AcidSepp/ArpEverywhere/pcb/arpEverywhere/arpEverywhere.kicad_sch

## KiCad design pcb/arpEverywhere/arpEverywhere.kicad_sch (2026-10-02)

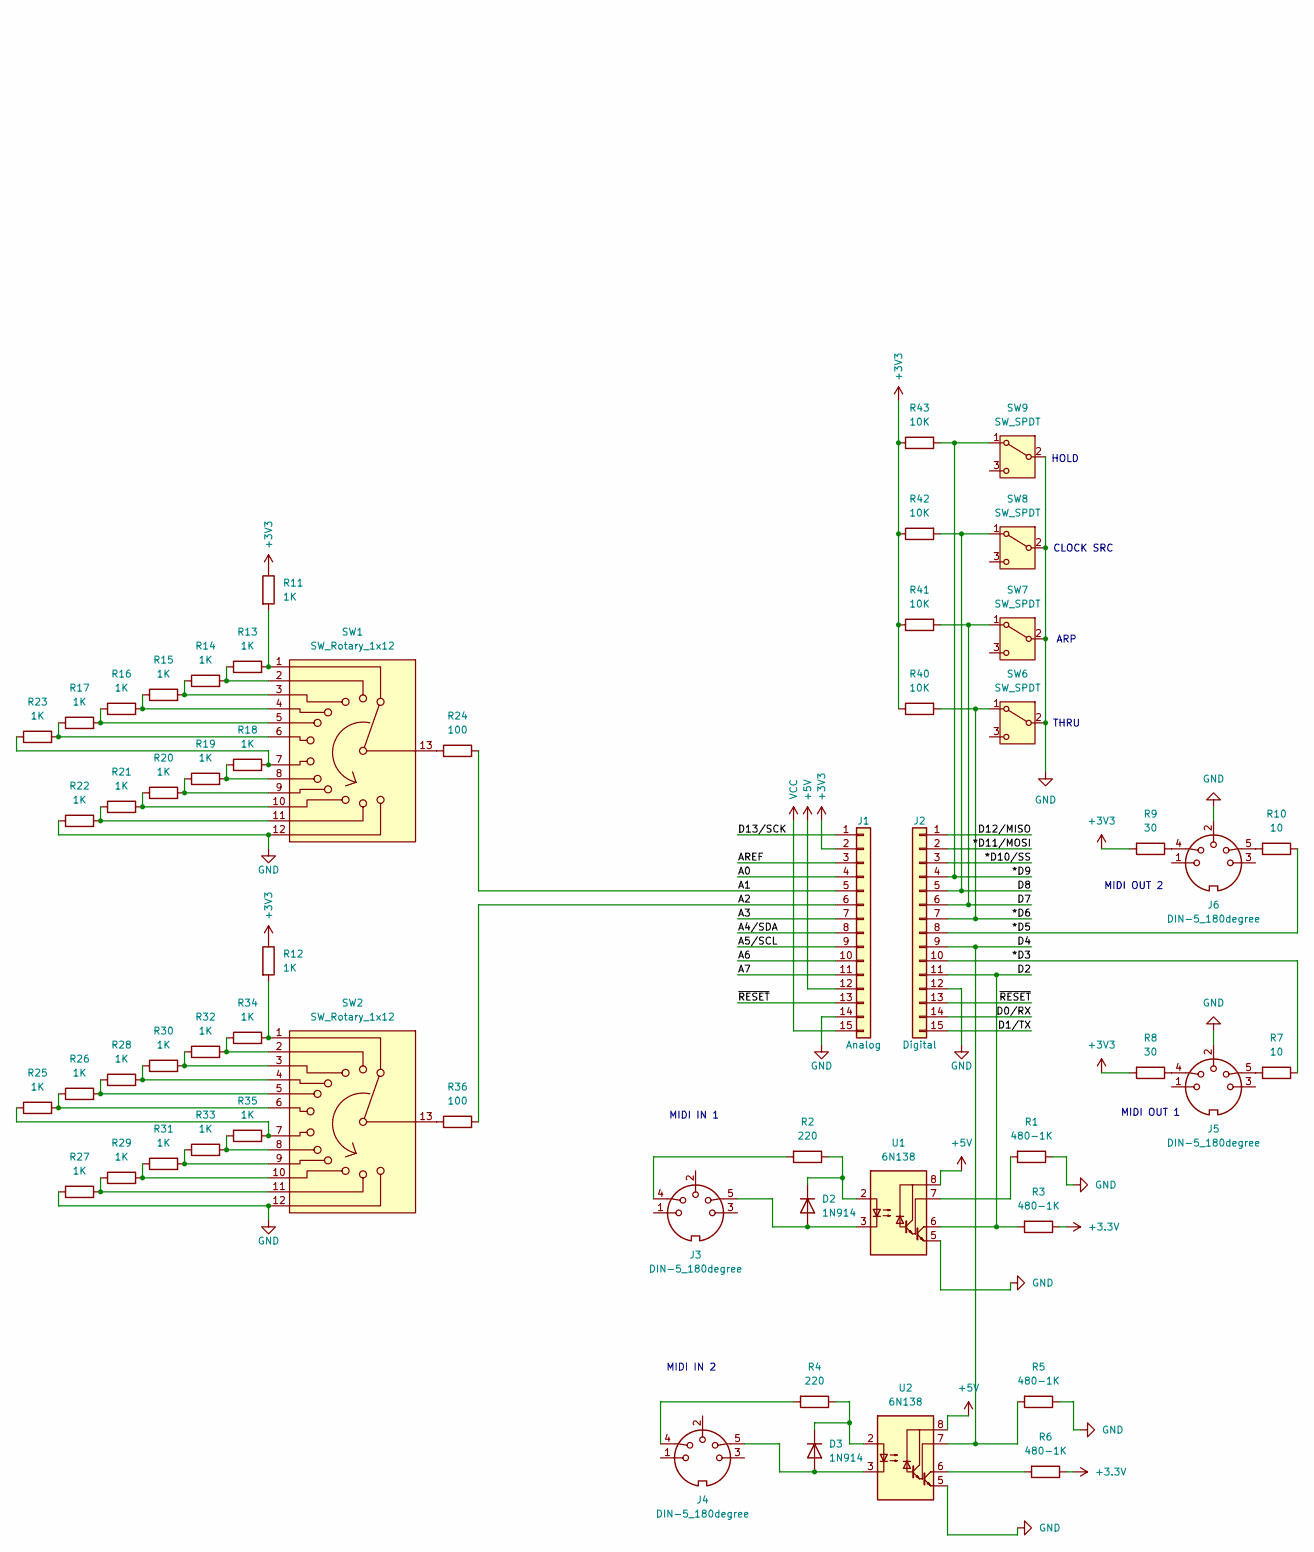
[picture p4: schematic arpEverywhere.kicad_sch, part in row 2, column 1]

Parts:
D2, D3: 1N914; D_DO-35_SOD27_P7.62mm_Horizontal
J1: Analog; PinHeader_1x15_P2.54mm_Vertical
J2: Digital; PinHeader_1x15_P2.54mm_Vertical
J3, J4, J5, J6: DIN-5_180degree; D_DO-35_SOD27_P7.62mm_Horizontal
R1, R3, R5, R6: 480-1K; DIP-8_W7.62mm
R2, R4: 220; DIP-8_W7.62mm
R7, R10: 10; DIP-8_W7.62mm
R8, R9: 30; DIP-8_W7.62mm
R11, R12, R13, R14, R15, R16, R17, R18, R19, R20, R21, R22, R23, R25, R26, R27, R28, R29, R30, R31, R32, R33, R34, R35: 1K
R24, R36: 100
R40, R41, R42, R43: 10K; DIP-8_W7.62mm
SW1, SW2: SW_Rotary_1x12
SW6, SW7, SW8, SW9: SW_SPDT; Nidec_Copal_CAS-120A
U1, U2: 6N138; SMDIP-8_W9.53mm

Connections:
+3.3V: R3.1, R6.1
+3V3: J1.2, R8.2, R9.2, R11.1, R12.1, R40.1, R41.1, R42.1, R43.1
+5V: J1.12, U1.8 (VCC), U2.8 (VCC)
A0: J1.4
A1: J1.5, R24.2
A2: J1.6, R36.2
A3: J1.7
A4/SDA: J1.8
A5/SCL: J1.9
A6: J1.10
A7: J1.11
AREF: J1.3
D0/RX: J2.14
D1/TX: J2.15
D2: J2.11, R3.2, U1.6 (VO2)
D4: J2.9, R5.2, U2.7 (VO1)
D7: J2.6, R41.2, SW7.1 (A)
D8: J2.5, R42.2, SW8.1 (A)
D12/MISO: J2.1
D13/SCK: J1.1
GND: J1.14, J2.12, J5.2, J6.2, R1.1, R5.1, R22.1, R27.1, SW1.12, SW2.12, SW6.2 (B), SW7.2 (B), SW8.2 (B), SW9.2 (B), U1.5 (GND), U2.5 (GND)
unnamed: D2.1 (K), R2.1, U1.2 (C1)
unnamed: D2.2 (A), J3.5, U1.3 (C2)
unnamed: D3.1 (K), R4.1, U2.2 (C1)
unnamed: D3.2 (A), J4.5, U2.3 (C2)
unnamed: J3.4, R2.2
unnamed: J4.4, R4.2
unnamed: J5.4, R8.1
unnamed: J5.5, R7.2
unnamed: J6.4, R9.1
unnamed: J6.5, R10.2
unnamed: R1.2, U1.7 (VO1)
unnamed: R6.2, U2.6 (VO2)
unnamed: R11.2, R13.2, SW1.1
unnamed: R12.2, R34.2, SW2.1
unnamed: R13.1, R14.2, SW1.2
unnamed: R14.1, R15.2, SW1.3
unnamed: R15.1, R16.2, SW1.4
unnamed: R16.1, R17.2, SW1.5
unnamed: R17.1, R23.2, SW1.6
unnamed: R18.1, R19.2, SW1.8
unnamed: R18.2, R23.1, SW1.7
unnamed: R19.1, R20.2, SW1.9
unnamed: R20.1, R21.2, SW1.10
unnamed: R21.1, R22.2, SW1.11
unnamed: R24.1, SW1.13
unnamed: R25.1, R35.2, SW2.7
unnamed: R25.2, R26.1, SW2.6
unnamed: R26.2, R28.1, SW2.5
unnamed: R27.2, R29.1, SW2.11
unnamed: R28.2, R30.1, SW2.4
unnamed: R29.2, R31.1, SW2.10
unnamed: R30.2, R32.1, SW2.3
unnamed: R31.2, R33.1, SW2.9
unnamed: R32.2, R34.1, SW2.2
unnamed: R33.2, R35.1, SW2.8
unnamed: R36.1, SW2.13
VCC: J1.15
d3: J2.10, R7.1
d5: J2.8, R10.1
d6: J2.7, R40.2, SW6.1 (A)
d9: J2.4, R43.2, SW9.1 (A)
d10/ss: J2.3
d11/mosi: J2.2
~RESET: J1.13, J2.13

Notes on the sheet:
MIDI OUT 2
MIDI IN 1
CLOCK SRC
MIDI IN 2
HOLD
THRU
MIDI OUT 1
ARP
