AcidSepp/ArpEverywhere/pcb/arpEverywhere/arpEverywhereWithConnectors.kicad_sch

## KiCad design pcb/arpEverywhere/arpEverywhereWithConnectors.kicad_sch (2026-10-06)

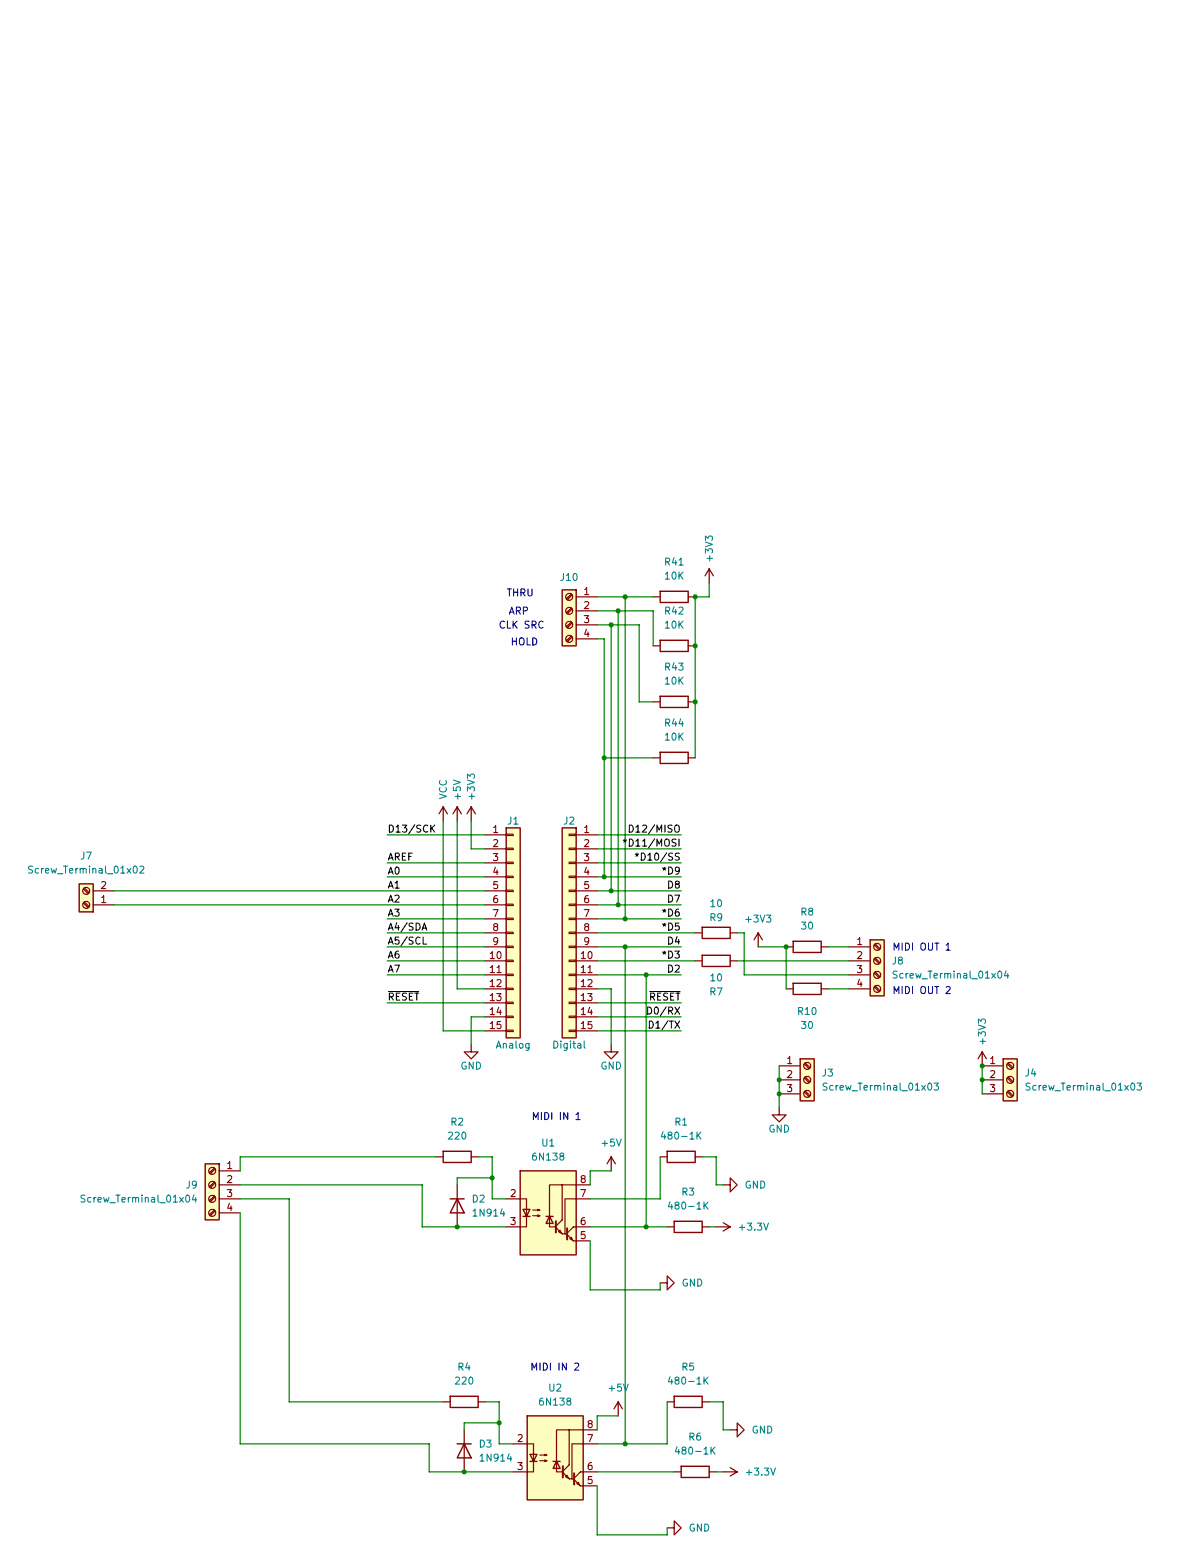
[picture p5: schematic arpEverywhereWithConnectors.kicad_sch, part in row 2, column 1]

Parts:
D2, D3: 1N914; D_DO-35_SOD27_P7.62mm_Horizontal
J1: Analog; PinHeader_1x15_P2.54mm_Vertical
J2: Digital; PinHeader_1x15_P2.54mm_Vertical
J3, J4: Screw_Terminal_01x03; WSON-8-1EP_6x5mm_P1.27mm_EP3.4x4mm
J7: Screw_Terminal_01x02
J8, J9, J10: Screw_Terminal_01x04
R1, R3, R5, R6: 480-1K; DIP-8_W7.62mm
R2, R4: 220; DIP-8_W7.62mm
R7, R9: 10; DIP-8_W7.62mm
R8, R10: 30; DIP-8_W7.62mm
R41, R42, R43, R44: 10K; DIP-8_W7.62mm
U1, U2: 6N138; SMDIP-8_W9.53mm

Connections:
+3.3V: R3.1, R6.1
+3V3: J1.2, J4.1, J4.2, J4.3, R8.2, R10.2, R41.1, R42.1, R43.1, R44.1
+5V: J1.12, U1.8 (VCC), U2.8 (VCC)
A0: J1.4
A1: J1.5, J7.2
A2: J1.6, J7.1
A3: J1.7
A4/SDA: J1.8
A5/SCL: J1.9
A6: J1.10
A7: J1.11
AREF: J1.3
D0/RX: J2.14
D1/TX: J2.15
D2: J2.11, R3.2, U1.6 (VO2)
D4: J2.9, R5.2, U2.7 (VO1)
D7: J2.6, J10.2, R42.2
D8: J2.5, J10.3, R43.2
D12/MISO: J2.1
D13/SCK: J1.1
GND: J1.14, J2.12, J3.1, J3.2, J3.3, R1.1, R5.1, U1.5 (GND), U2.5 (GND)
unnamed: D2.1 (K), R2.1, U1.2 (C1)
unnamed: D2.2 (A), J9.2, U1.3 (C2)
unnamed: D3.1 (K), R4.1, U2.2 (C1)
unnamed: D3.2 (A), J9.4, U2.3 (C2)
unnamed: J8.1, R8.1
unnamed: J8.2, R7.1
unnamed: J8.3, R9.1
unnamed: J8.4, R10.1
unnamed: J9.1, R2.2
unnamed: J9.3, R4.2
unnamed: R1.2, U1.7 (VO1)
unnamed: R6.2, U2.6 (VO2)
VCC: J1.15
d3: J2.10, R7.2
d5: J2.8, R9.2
d6: J2.7, J10.1, R41.2
d9: J2.4, J10.4, R44.2
d10/ss: J2.3
d11/mosi: J2.2
~RESET: J1.13, J2.13

Notes on the sheet:
MIDI OUT 2
MIDI IN 1
MIDI IN 2
CLK SRC
THRU
MIDI OUT 1
ARP
HOLD
