AcidSepp/ArpEverywhere/include/Random4.h

//
// Created by yannick on 9/26/26.
//

#ifndef ARPEVERYWHERE_RANDOM4_H
#define ARPEVERYWHERE_RANDOM4_H


class Random4 {

public:
    Random4();

    static int next(int sustainedNoteCount);
};


#endif //ARPEVERYWHERE_RANDOM4_H
