AcidSepp/ArpEverywhere/include/Random1.h

//
// Created by yannick on 9/26/26.
//

#ifndef ARPEVERYWHERE_RANDOM1_H
#define ARPEVERYWHERE_RANDOM1_H


class Random1 {
public:
    Random1();

    static int next(int sustainedNoteCount);
};


#endif //ARPEVERYWHERE_RANDOM1_H
