AcidSepp/ArpEverywhere/include/rotarySwitch.h

#ifndef ARPEVERYWHERE_ROTARYSWITCH_H
#define ARPEVERYWHERE_ROTARYSWITCH_H

#ifdef __cplusplus
extern "C" {
#endif

int getRotarySwitchNumber(int sensorValue);

#ifdef __cplusplus
}
#endif

#endif //ARPEVERYWHERE_ROTARYSWITCH_H
